piotr-sb/PSB_Xmas_Tree/doc/assets/IMG_20211105_203522135.jpg

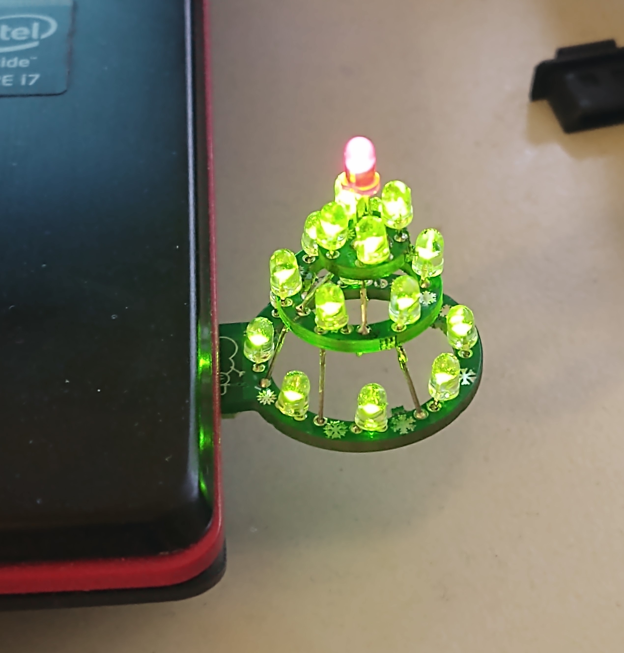
doc/assets/IMG_20211105_203522135.jpg
